New-Legends/NBUT_super_cap/user_code/task/communicate.h

/**
 * @file communicate.h
 * @author NBUT NJY
 * @brief 
 * @version 0.1
 * @date 2022-11-26
 * 
 * @copyright Copyright (c) 2022
 * 
 */
#ifndef COMMUNICATE_H
#define COMMUNICATE_H

#include "main.h"
#include "FreeRTOS.h"
#include "bsp_ina226.h"
#include "tim.h"
#include "bsp_can.h"
#include "can_receive.h"
#include "can.h"

#endif
