New-Legends/NBUT_super_cap/user_code/bsp/bsp_LM5106.h

/**
 * @file bsp_LM5106.h
 * @author NJY
 * @brief 
 * @version 0.1
 * @date 2022-11-23
 * 
 * @copyright Copyright (c) 2022
 * 
 */
#ifndef BSP_LM5106_H
#define BSP_LM5106_H

#include "gpio.h"
#include "main.h"
#include "struct_typedef.h"

void CAP_CHARGE_ON(void);
void CAP_CHARGE_OFF(void);

#endif
